andyw-lala/Tek7904ALedGraticule/images/PXL_20210615_022417282.jpg

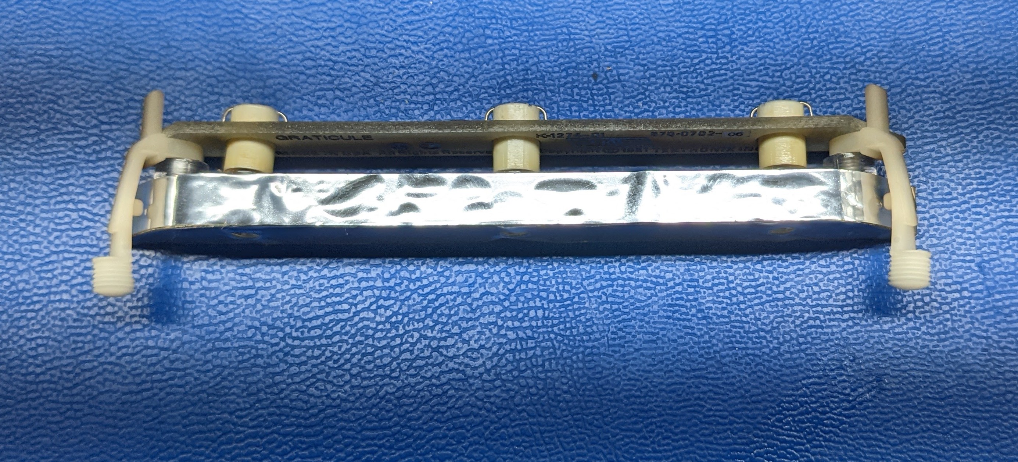
images/PXL_20210615_022417282.jpg
