andyw-lala/Tek7904ALedGraticule/images/PXL_20210615_022752127.jpg

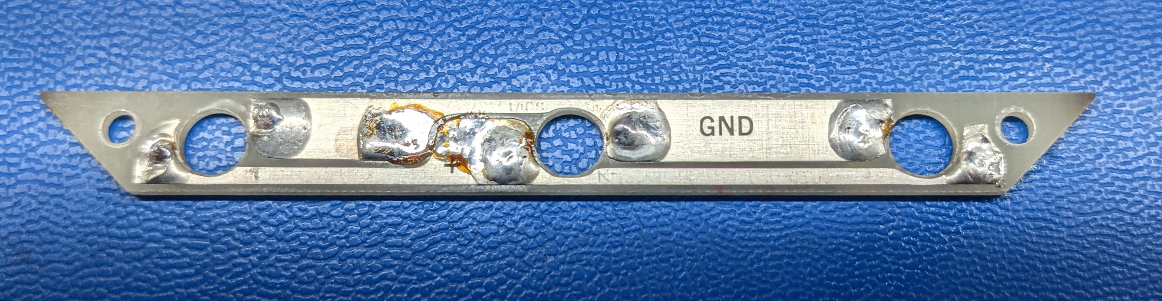
images/PXL_20210615_022752127.jpg
