andyw-lala/Tek7904ALedGraticule/images/PXL_20210615_023820695.jpg

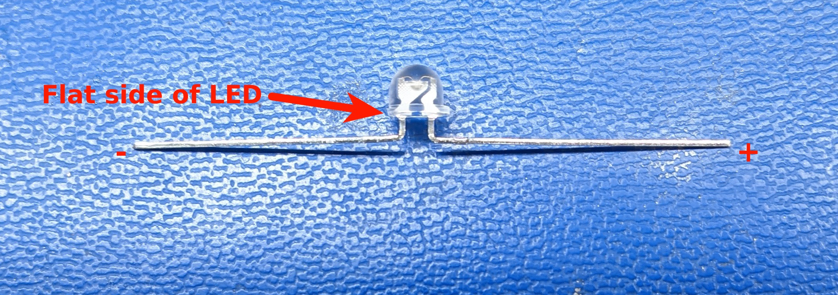
images/PXL_20210615_023820695.jpg
