andyw-lala/Tek7904ALedGraticule/images/PXL_20210615_024128291.jpg

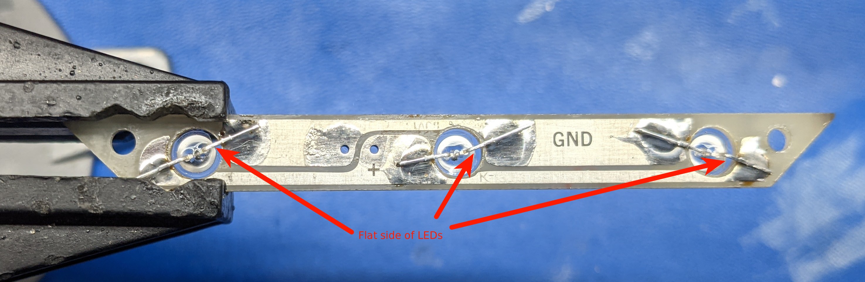
images/PXL_20210615_024128291.jpg
