andyw-lala/Tek7904ALedGraticule/images/PXL_20210615_024433127.jpg

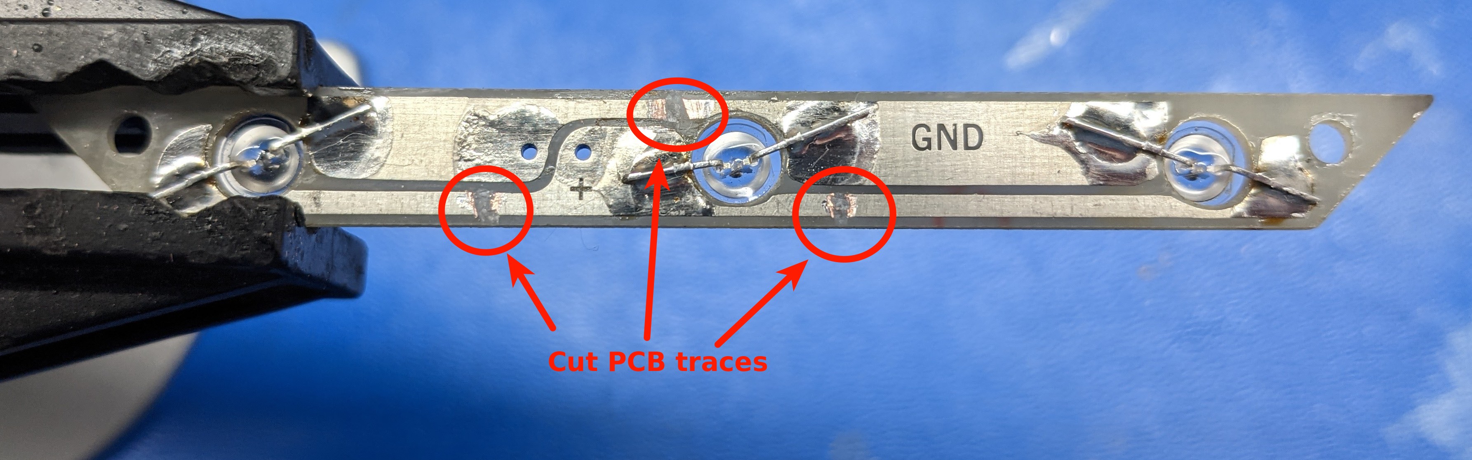
images/PXL_20210615_024433127.jpg
