andyw-lala/Tek7904ALedGraticule/images/PXL_20210615_024639665.jpg

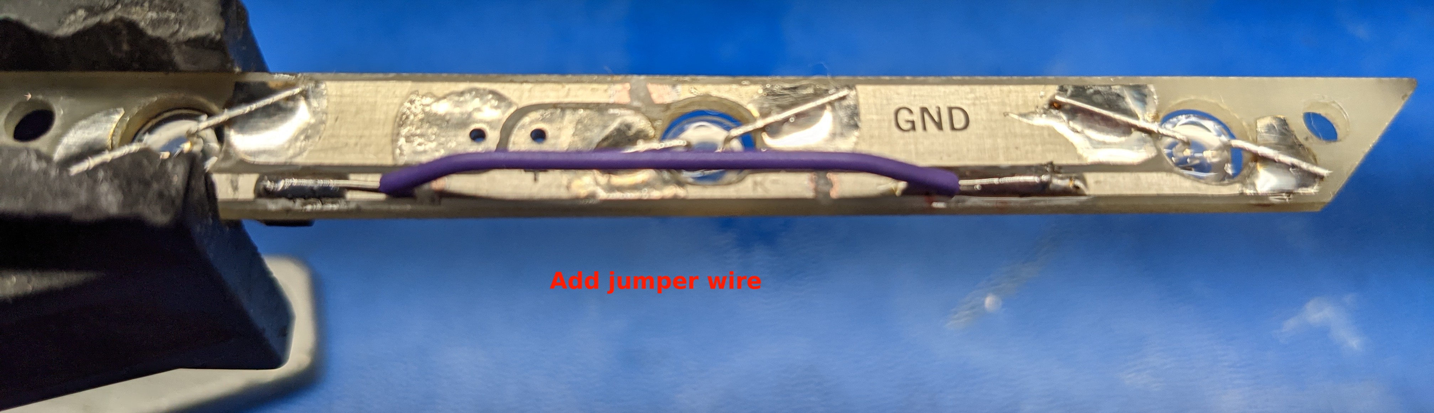
images/PXL_20210615_024639665.jpg
