andyw-lala/Tek7904ALedGraticule/images/PXL_20210720_014014225.jpg

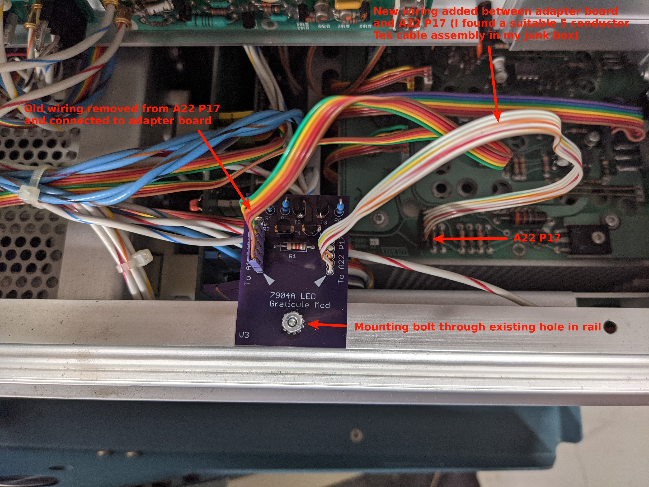
images/PXL_20210720_014014225.jpg
