andyw-lala/Tek7904ALedGraticule/images/PXL_20220108_233952439.jpg

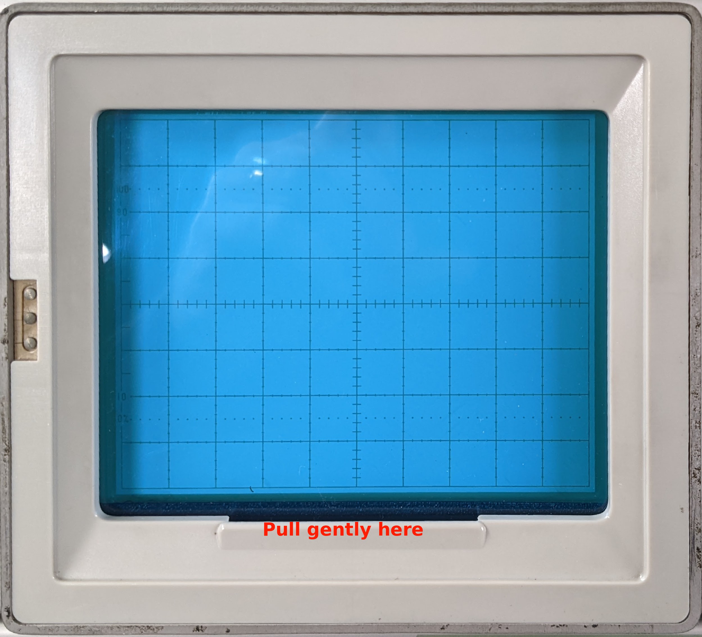
images/PXL_20220108_233952439.jpg
