andyw-lala/Tek7904ALedGraticule/images/PXL_20220108_234001968.jpg

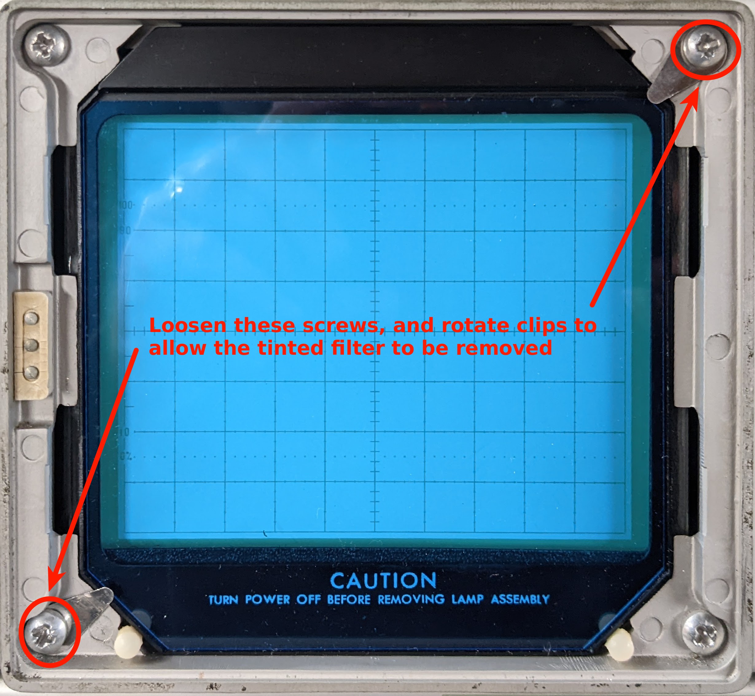
images/PXL_20220108_234001968.jpg
