andyw-lala/Tek7904ALedGraticule/images/PXL_20220108_234047702.jpg

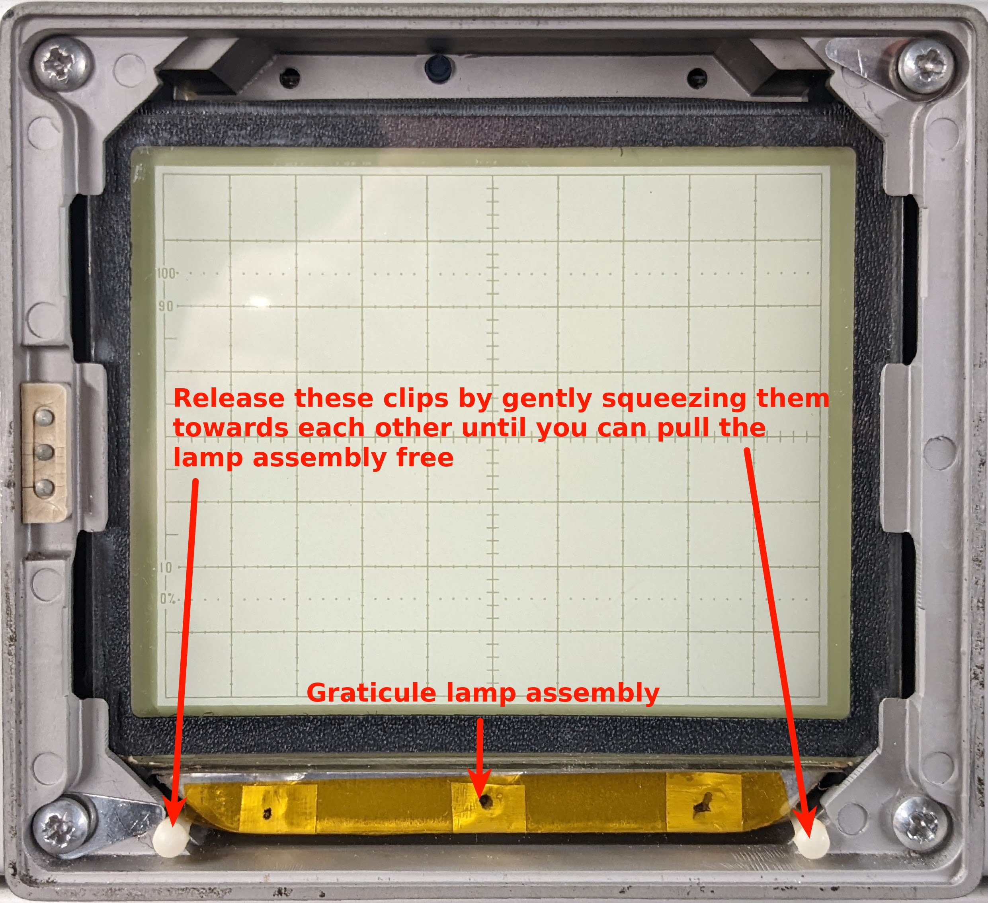
images/PXL_20220108_234047702.jpg
