andyw-lala/Tek7904ALedGraticule/images/PXL_20220108_234137003.jpg

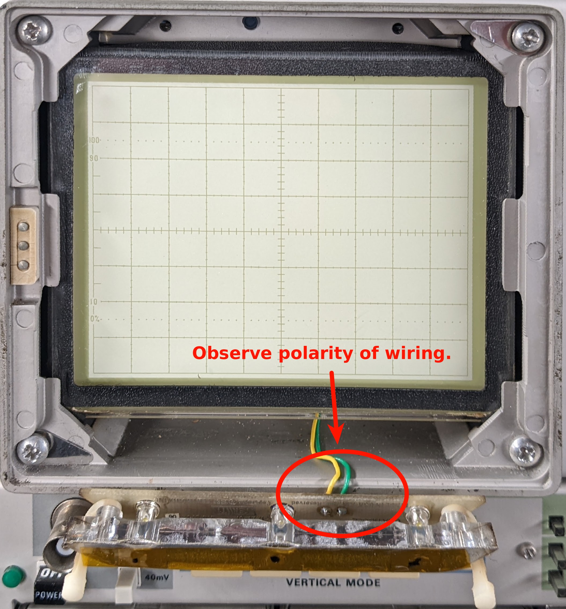
images/PXL_20220108_234137003.jpg
